robotmindio/RobotSkin/scad/09_cable_clip.scad

include <rm_common.scad>

// Grove cable clip carrier; the hex plug is printed into its underside.
CABLE_W=7.5;
CABLE_H=2.2;
BASE=24;

module cable_clip_carrier() {
  carrier_mount() {
    difference() {
      translate([-BASE/2,-BASE/2,0]) rounded_box([BASE,BASE,4],2);
      translate([0,0,2.8]) cube([CABLE_W,CABLE_H+1,4],center=true);
      translate([0,BASE/2-3,2.8]) cube([CABLE_W,7,4],center=true);
    }
  }
}

print_on_y_edge(BASE) cable_clip_carrier();
