robotmindio/RobotSkin/scad/parts/angle_join.scad

include <../lib/robotskin.scad>
angle_join();
