robotmindio/RobotSkin/scad/parts/din_rail_adapter.scad

include <../lib/robotskin.scad>
din_rail_adapter();
