robotmindio/RobotSkin/scad/parts/double_sided_plate_4x1.scad

include <../lib/robotskin.scad>
double_sided_plate(4,1);
