robotmindio/RobotSkin/scad/parts/esp32_s3_devkitc_carrier.scad

include <../lib/robotskin.scad>
translate([0,0,RM_ESP32_S3_DEVKITC_BODY_SIZE[1]/2])
  rotate([90,0,0]) esp32_s3_devkitc_carrier();
