robotmindio/RobotSkin/scad/parts/flat_join.scad

include <../lib/robotskin.scad>
flat_join();
