robotmindio/RobotSkin/scad/parts/grove_cable_clip.scad

include <../lib/robotskin.scad>
grove_cable_clip();
