robotmindio/RobotSkin/scad/parts/grove_carrier_40x40.scad

include <../lib/robotskin.scad>
grove_carrier([40,40]);
