robotmindio/RobotSkin/scad/parts/grove_carrier_40x60.scad

include <../lib/robotskin.scad>
grove_carrier([40,60]);
