robotmindio/RobotSkin/scad/parts/grove_carrier_4x2.scad

include <../lib/robotskin.scad>
grove_carrier_4x2();
