robotmindio/RobotSkin/scad/parts/grove_lcd_16x2_carrier.scad

include <../lib/robotskin.scad>
grove_lcd_16x2_carrier();
