robotmindio/RobotSkin/scad/parts/grove_plaque.scad

include <../lib/robotmind.scad>
grove_plaque();
