robotmindio/RobotSkin/scad/parts/h25t_horn_plate_3x3.scad

include <../lib/robotskin.scad>

h25t_horn_plate_3x3();
