robotmindio/RobotSkin/scad/parts/h25t_port_cube_3x3.scad

include <../lib/robotskin.scad>

h25t_port_cube_3x3();
