robotmindio/RobotSkin/scad/parts/ld06_pj030_clamp_bar.scad

include <../lib/robotskin.scad>
ld06_pj030_clamp_bar();
