robotmindio/RobotSkin/scad/parts/lekiwi-lidar-base.scad

include <../lib/robotskin.scad>
lekiwi_lidar_base();
