robotmindio/RobotSkin/scad/parts/outer_angle_join.scad

include <../lib/robotskin.scad>
outer_angle_join();
