robotmindio/RobotSkin/scad/parts/plate_4x2.scad

include <../lib/robotskin.scad>
plate(4,2);
