robotmindio/RobotSkin/scad/parts/plate_8x8.scad

include <../lib/robotskin.scad>
plate(8,8);
