robotmindio/RobotSkin/scad/parts/profile_2020_adapter.scad

include <../lib/robotskin.scad>
profile_2020_adapter();
