robotmindio/RobotSkin/scad/parts/rpi5_usb_carrier.scad

include <../lib/robotskin.scad>
rpi5_usb_carrier();
