robotmindio/RobotSkin/scad/parts/through_plate_12x10.scad

include <../lib/robotskin.scad>
through_plate(12,10);
