robotmindio/RobotSkin/scad/parts/through_plate_5x8.scad

include <../lib/robotskin.scad>
through_plate(5,8);
