robotmindio/RobotSkin/scad/parts/through_plate_8x8.scad

include <../lib/robotskin.scad>
through_plate(8,8);
