robotmindio/RobotSkin/scad/parts/tripod_adapter.scad

include <../lib/robotskin.scad>
tripod_adapter();
