robotmindio/RobotSkin/scad/source/universal_dock.scad

include <rm_common.scad>
universal_dock();
