robotmindio/RobotSkin/scad/00_fit_tests.scad

include <rm_common.scad>

PART="port"; // port, peg_small, peg_nominal or peg_large
assert(PART=="port" || PART=="peg_small" || PART=="peg_nominal" ||
       PART=="peg_large", "Unknown fit-test part");

module port_coupon() {
  coupon_t=RM_PORT_PILOT_DEPTH+2;
  difference() {
    cylinder(h=coupon_t,d=12);
    blind_port_cut();
  }
}

module peg_coupon(delta=0) {
  union() {
    cylinder(h=RM_LINK_T,d=10);
    translate([0,0,RM_LINK_T]) mount_peg(delta);
  }
}

if(PART=="port") port_coupon();
if(PART=="peg_small") peg_coupon(-0.1);
if(PART=="peg_nominal") peg_coupon();
if(PART=="peg_large") peg_coupon(0.1);
