robotmindio/RobotSkin/scad/test/alignment.scad

include <../lib/robotskin.scad>

assert(grid_size(8) == 80 && grid_size(3) == 30,
       "Plate size must be derived from its port count");
assert(2*RM_PLATE_T == 8 && RM_STS3215_HUB_RADIUS == 7,
       "The H25T horn plate must remain a double-thickness 3x3 interface");
assert(grid_size(3) == 30 && RM_M3_CLEARANCE < RM_INSERT_BORE,
       "The H25T hub must retain its 30 mm body and M3 lock paths");
assert(grid_positions(2) == [-5,5] &&
       grid_positions(3) == [-10,0,10] &&
       grid_positions(8) == [-35,-25,-15,-5,5,15,25,35],
       "Every grid must remain centred at 10 mm pitch");
assert(edge_rows(2) == [5,15] && flat_rows(2) == [-15,-5,5,15],
       "Join rows must derive from their depth port count");
assert(outer_rows(2) == [9,19],
       "Outer joins must offset their rows by plate thickness");
assert(is_corner_index(0,0,8,8) && is_corner_index(7,7,8,8) &&
       is_corner_index(2,4,3,5) && !is_corner_index(1,1,3,5),
       "Corner mounting ports must work for every plate size");
lcd_holes = centred_points(RM_GROVE_LCD_16X2_HOLES,RM_GROVE_LCD_16X2_SIZE);
assert(RM_GROVE_GESTURE_SIZE == [20,20] &&
       RM_GROVE_GESTURE_HOLES == [[0,-10],[0,10]],
       "Grove Gesture 2x2 footprint must retain its two 20 mm-spaced holes");
assert(RM_GROVE_IMU_9DOF_SIZE == [40,20] &&
       RM_GROVE_IMU_9DOF_HOLES == [[-20,0],[10,-10],[10,10]],
       "Grove IMU 9DOF 4x2 footprint must retain its three-hole pattern");
assert(2*15+octagon_d(peg_root_af()) <= RM_GROVE_IMU_9DOF_SIZE[0],
       "Grove 4x2 locks must stay within the 40 mm PCB length");
assert(RM_PJ030_SIZE == [40,20] && RM_PJ030_PCB_T == 1.6,
       "PJ030 controller clamp must retain its 40 x 20 x 1.6 mm PCB envelope");
assert(2*5+octagon_d(peg_root_af()) <= RM_PJ030_SIZE[0],
       "PJ030 locks must stay within the 40 mm PCB length");
assert(RM_PJ030_SIZE[1] == 2*RM_GRID,
       "PJ030 clamp bases must span two 10 mm grid pitches");
assert(RM_PJ030_CLAMP_T > RM_LOCK_SCREW_LENGTH-RM_INSERT_DEPTH &&
       RM_PJ030_CLAMP_PRELOAD > 0,
       "PJ030 clamp screws must engage without bottoming in their inserts");
assert(RM_GROVE_LCD_16X2_SIZE == [80,40] &&
       lcd_holes == [[-38,-18],[38,-18],[-38,18],[38,18]],
       "Grove 16x2 LCD footprint must retain its 76 x 36 mm hole pattern");
assert(grid_station_outside(31) == 35 && grid_station_outside(28) == 35,
       "External lock stations must remain on the RobotSkin grid");
assert(RM_TRIPOD_BODY_T-RM_TRIPOD_NUT_H >= 2,
       "Tripod nut pocket must retain a structural roof");
uno_holes = centred_points(RM_UNO_HOLES,RM_UNO_SIZE);
assert(near(uno_holes[0][0],-20.29) && near(uno_holes[0][1],-24.13) &&
       near(uno_holes[2][0],31.75) && near(uno_holes[2][1],8.89),
       "UNO mounting holes must retain the official asymmetric layout");
assert(RM_UNO_LOCK_X+RM_GRID/2 < RM_UNO_SIZE[0]/2 &&
       RM_UNO_LOCK_Y+RM_GRID/2 < RM_UNO_SIZE[1]/2,
       "UNO RobotSkin locks must remain hidden below the board");
assert(RM_RPI5_SIZE == [85,56] &&
       RM_WAVESHARE_USB_C_SIZE == [87,37.5] &&
       RM_WAVESHARE_USB_C_HOLE_SPACING == [58,30.5],
       "Raspberry Pi 5 and Waveshare Board (C) footprints must remain exact");
assert(RM_RPI5_USB_CARRIER_SIZE[0] >=
       RM_RPI5_SIZE[1]+RM_RPI5_USB_GAP+RM_WAVESHARE_USB_C_SIZE[1] &&
       RM_RPI5_USB_CARRIER_SIZE[1] >=
       RM_WAVESHARE_USB_C_HOLE_SPACING[0]+RM_RPI5_USB_STANDOFF_D,
       "Raspberry Pi 5 carrier must span both PCBs and standoff rows");
assert(len(rpi5_usb_locks()) == 8 &&
       len(waveshare_usb_c_holes()) == 4,
       "Raspberry Pi 5 carrier needs eight RobotSkin locks and four USB-board mounts");
assert(near(-39+RM_GRID/2,-29-RM_GRID/2) &&
       near(19+RM_GRID/2,29-RM_GRID/2),
       "Raspberry Pi 5 and Waveshare screw rows must stay aligned");
assert(RM_RPI5_USB_CARRIER_SIZE[1] ==
       RM_WAVESHARE_USB_C_HOLE_SPACING[0]+RM_RPI5_USB_STANDOFF_D+1,
       "Raspberry Pi 5 carrier must keep only 0.5 mm beyond each standoff row");
assert(RM_RPI5_TABLE_SIZE == [grid_size(12),grid_size(10)] &&
       len(rpi5_table_locks()) == 4,
       "Raspberry Pi 5 table must cover the assembly on four RobotSkin locks");
assert(RM_RPI5_TABLE_CLEARANCE >=
       RM_CARRIER_T+RM_RPI5_USB_STANDOFF_H+1.6+13.7+5,
       "Raspberry Pi 5 table must clear the PCB and active cooler with airflow space");
for(position=rpi5_table_locks())
  assert(abs(position[0])-RM_RPI5_TABLE_LEG_D/2 >=
         RM_RPI5_USB_CARRIER_SIZE[0]/2,
         "Raspberry Pi 5 table legs must remain outside the carrier");
assert(RM_ESP32_S3_DEVKITC_HEADER_SPACING-
       RM_ESP32_S3_DEVKITC_HEADER_W == 22 &&
       RM_ESP32_S3_DEVKITC_HEADER_SPACING+
       RM_ESP32_S3_DEVKITC_HEADER_W == 28 &&
       RM_ESP32_S3_DEVKITC_HEADER_H == 2,
       "ESP32 header bodies must match the user's three caliper measurements");
assert(RM_ESP32_S3_DEVKITC_SNAP_OVERLAP > 0 &&
       RM_ESP32_S3_DEVKITC_SNAP_GAP > 0 &&
       esp32_s3_hook_tip() > RM_ESP32_S3_DEVKITC_HEADER_SPACING/2+2.54/2,
       "Hooks must retain plastic above the PCB and clear nominal jumper housings");
assert(esp32_s3_devkitc_locks() ==
       [[-15,0],[-5,0],[5,0],[15,0]],
       "ESP32-S3 carrier must keep one continuous 10 mm lock row");
assert(RM_TEST_MALE_FITS == [0,0.05,0.10,0.15,0.20],
       "Tolerance coupon must retain its documented five male fits");
assert(RM_TEST_INSERT_BORES == [3.75,3.80,3.85,3.90,3.95],
       "Insert coupon must retain its documented five pilot bores");
for(bore=RM_TEST_INSERT_BORES)
  assert(bore < RM_INSERT_OD && bore > RM_M3_CLEARANCE,
         "Every insert pilot must be below insert OD and above M3 clearance");
for(fit=RM_TEST_MALE_FITS)
  assert(peg_root_af(fit) > port_af(0) && port_af(0) > peg_tip_af(fit),
         "Every coupon peg must fit the nominal female port");

// Small alternate instances keep the parameterized public API executable.
plate(2,3);
translate([0,-50,0]) plate(3,3,thickness=2*RM_PLATE_T);
translate([50,-50,0]) h25t_horn_plate_3x3();
translate([100,-50,0]) h25t_port_cube_3x3();
translate([0,50,0]) through_plate(5,3);
translate([0,100,0]) through_plate(5,8);
translate([70,100,0]) double_sided_plate(4,1);
translate([30,0,0]) flat_join(1,1);
translate([50,0,0]) angle_join(1,1);
translate([75,0,0]) outer_angle_join(1,1);
translate([100,20,0]) grove_carrier_2x2();
translate([100,45,0]) grove_carrier_4x2();
translate([100,70,0]) grove_lcd_16x2_carrier();
translate([170,10,0]) ld06_pj030_clamp_base();
translate([170,30,0]) rotate([0,0,180]) ld06_pj030_clamp_base();
translate([170,10,RM_CARRIER_T+RM_PJ030_PCB_T-RM_PJ030_CLAMP_PRELOAD])
  ld06_pj030_clamp_bar();
translate([170,30,RM_CARRIER_T+RM_PJ030_PCB_T-RM_PJ030_CLAMP_PRELOAD])
  rotate([0,0,180]) ld06_pj030_clamp_bar();
translate([190,60,0]) tripod_adapter();
translate([230,60,0]) profile_2020_adapter();
translate([270,60,0]) din_rail_adapter();
translate([310,60,0]) grove_cable_clip();
translate([380,100,0]) uno_carrier();
translate([500,100,0]) rpi5_usb_carrier();
translate([650,100,0]) rpi5_table();
translate([780,100,0]) esp32_s3_devkitc_carrier();
translate([100,0,0]) connector_grid(2,2,direction="up");
translate([130,0,0])
  difference() {
    cube([grid_size(2),grid_size(2),RM_PLATE_T],center=true);
    connector_grid(2,2,direction="up",cut=true,body_t=RM_PLATE_T);
  }

assert(RM_POGO_FACE_T == 0.8 && RM_POGO_FACE_SIZE == [60,18] && near(RM_POGO_SIZE[1],14.1) &&
       RM_POGO_SIZE[2] == 21 &&
       RM_POGO_PIN_PITCH == 20 && RM_POGO_PIN_HOLE_D > RM_POGO_PIN_D,
       "Pogo face must retain its compact envelope and clear both contacts");
assert(RM_POGO_MOUNT_PITCH == 43 &&
       RM_POGO_POST_D < RM_POGO_MOUNT_HOLE_D &&
       (RM_POGO_POST_D-RM_POGO_PILOT_D)/2 >= 1.2 &&
       RM_POGO_POST_H < RM_POGO_FLANGE_SIZE[2],
       "Pogo locating posts must fit flange holes with printable screw walls");
assert(RM_POGO_PILOT_FLOOR > RM_POGO_FACE_T &&
       RM_POGO_FACE_T+RM_POGO_FLANGE_SIZE[2]+0.3-3 > RM_POGO_PILOT_FLOOR,
       "M2x3 screws through 0.3 mm washers must not break through the face");
assert(RM_POGO_LOCK_COUNT == 6 &&
       grid_positions(RM_POGO_LOCK_COUNT) == [-25,-15,-5,5,15,25],
       "Pogo mount needs one uninterrupted standard 10 mm peg row");
assert(near(RM_POGO_LOCK_Y-RM_GRID/2,RM_POGO_RIM_DEPTH),
       "The rear rail must meet the rim directly, without spacer bridges");
assert(RM_POGO_PIN_Z-RM_POGO_REAR_BODY[2]/2-
       (RM_JOIN_T-RM_POGO_LOCK_RECESS+2.4) >= 0.5 &&
       RM_LOCK_SCREW_LENGTH-(RM_JOIN_T-RM_POGO_LOCK_RECESS) < RM_INSERT_DEPTH,
       "Recessed heads must clear the body without bottoming the M3x6 locks");
translate([870,100,0]) pogo_pin_mount();
