robotmindio/RobotSkin/scad/test_parts/tolerance_female_2x2.scad

include <../lib/robotskin.scad>
tolerance_female_tile();
