robotmindio/RobotSkin/scad/test_parts/tolerance_insert_set.scad

include <../lib/robotskin.scad>
tolerance_insert_set();
