robotmindio/RobotSkin/scad/test_parts/tolerance_male.scad

include <../lib/robotskin.scad>
tolerance_male_set();
